SuperHouse/PCBCONVEYOR/Mechanical/Belt Idler Conveyor v6.3mf

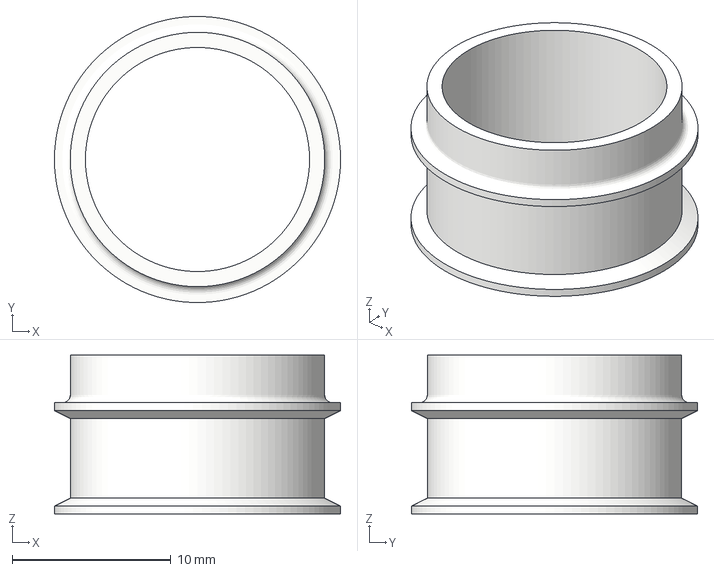
[picture p20: CAD file, 2022-12-20]
Mechanical/Belt Idler Conveyor v6.3mf
18.0 x 18.0 x 10.0 mm
