SuperHouse/PCBCONVEYOR/Mechanical/Front Rail Hole Drilling Template.3mf

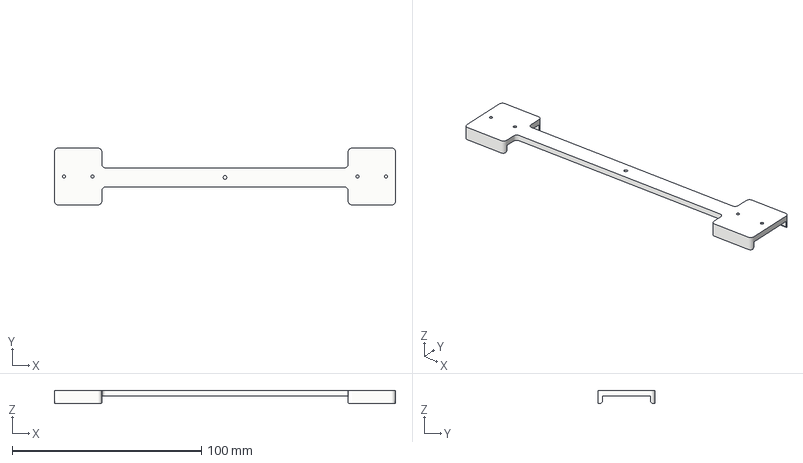
[picture p21: CAD file, 2022-12-20]
Mechanical/Front Rail Hole Drilling Template.3mf
180.0 x 30.0 x 7.00 mm
