SuperHouse/PCBCONVEYOR/Mechanical/GT2 Timing Belt Clamp.3mf

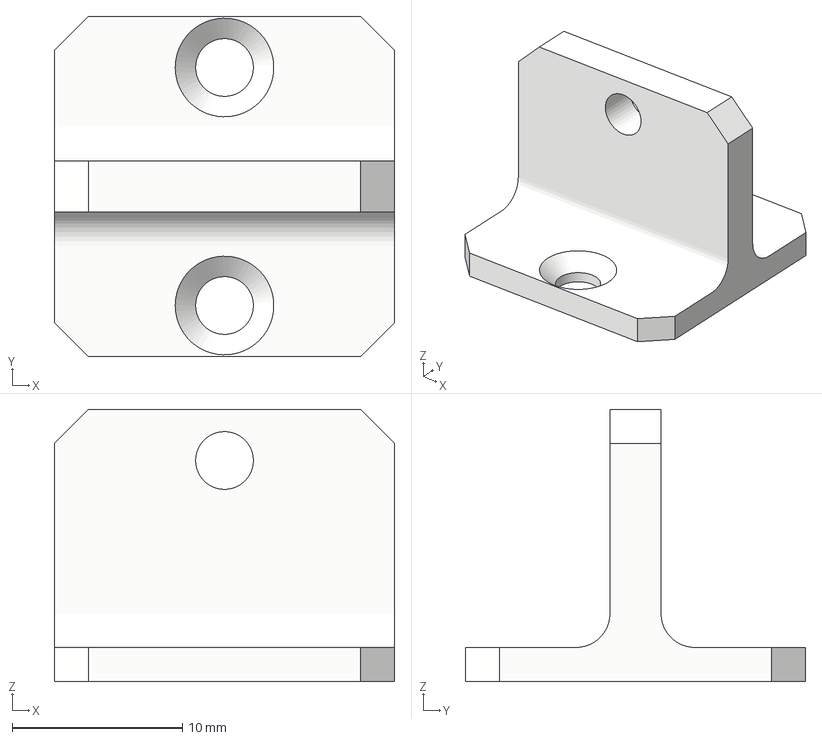
[picture p22: CAD file, 2022-12-20]
Mechanical/GT2 Timing Belt Clamp.3mf
20.0 x 20.0 x 16.0 mm
