SuperHouse/PCBCONVEYOR/Mechanical/PCB Holder PCBCONVEYOR.3mf

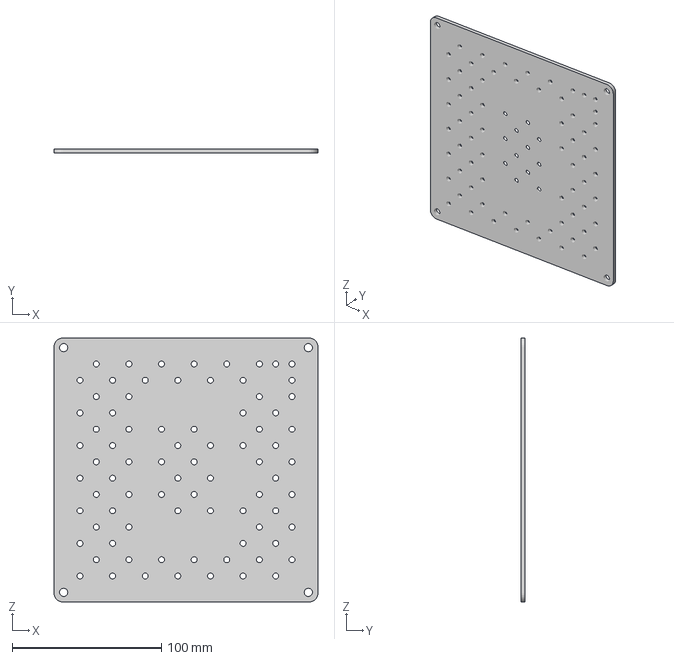
[picture p23: CAD file, 2022-12-20]
Mechanical/PCB Holder PCBCONVEYOR.3mf
177.0 x 3.00 x 177.0 mm
