SuperHouse/PCBCONVEYOR/Mechanical/Limit Switch Cover.3mf

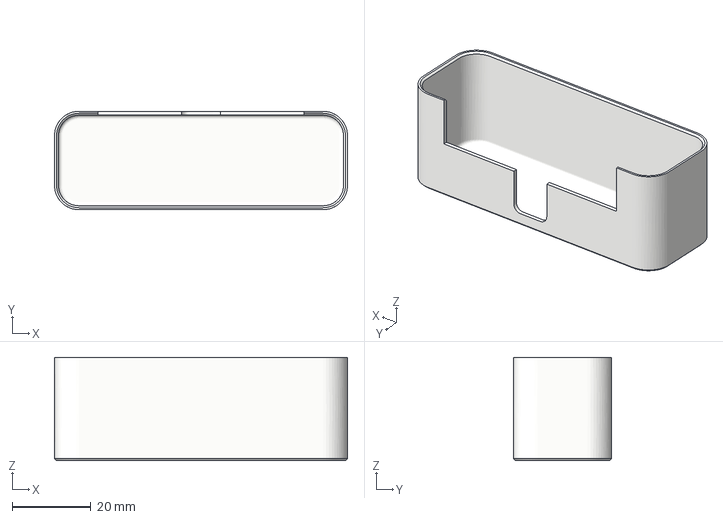
[picture p24: CAD file, 2022-12-20]
Mechanical/Limit Switch Cover.3mf
74.4 x 25.0 x 26.2 mm
