SuperHouse/PCBCONVEYOR/Mechanical/Y Axis Idler Clevis.3mf

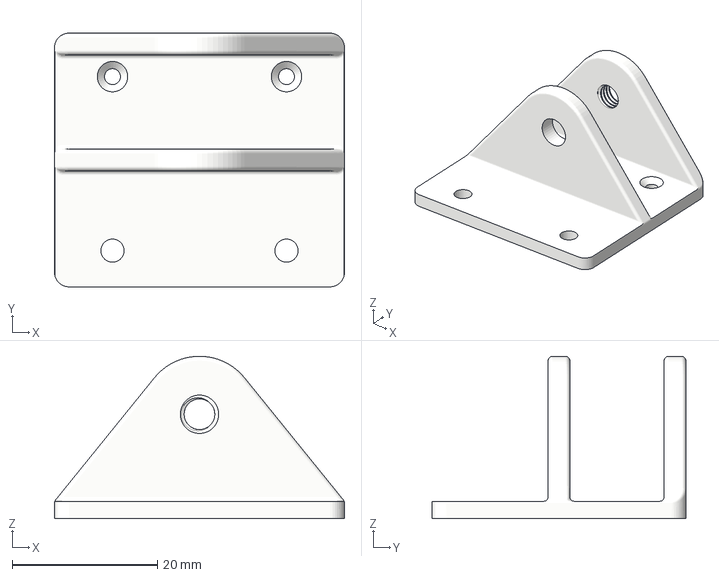
[picture p25: CAD file, 2022-12-20]
Mechanical/Y Axis Idler Clevis.3mf
40.0 x 35.0 x 22.4 mm
