SuperHouse/PCBCONVEYOR/Mechanical/GT2 Timing Belt Clamp Cover.3mf

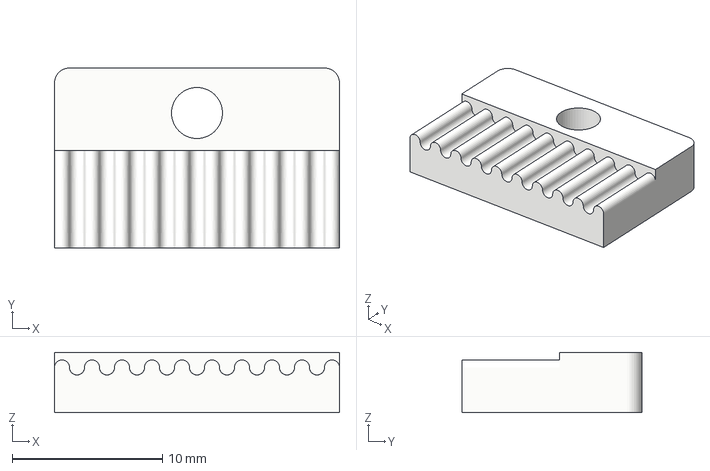
[picture p26: CAD file, 2022-12-20]
Mechanical/GT2 Timing Belt Clamp Cover.3mf
19.0 x 12.0 x 4.00 mm
