SuperHouse/PCBCONVEYOR/Mechanical/Limit Switch Mount.3mf

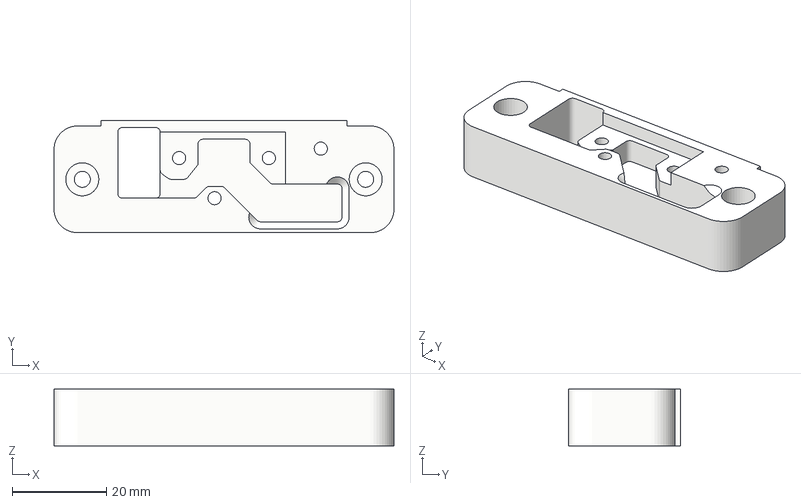
[picture p27: CAD file, 2022-12-20]
Mechanical/Limit Switch Mount.3mf
72.0 x 23.8 x 12.0 mm
