SuperHouse/PCBCONVEYOR/Mechanical/Sensor Probe.3mf

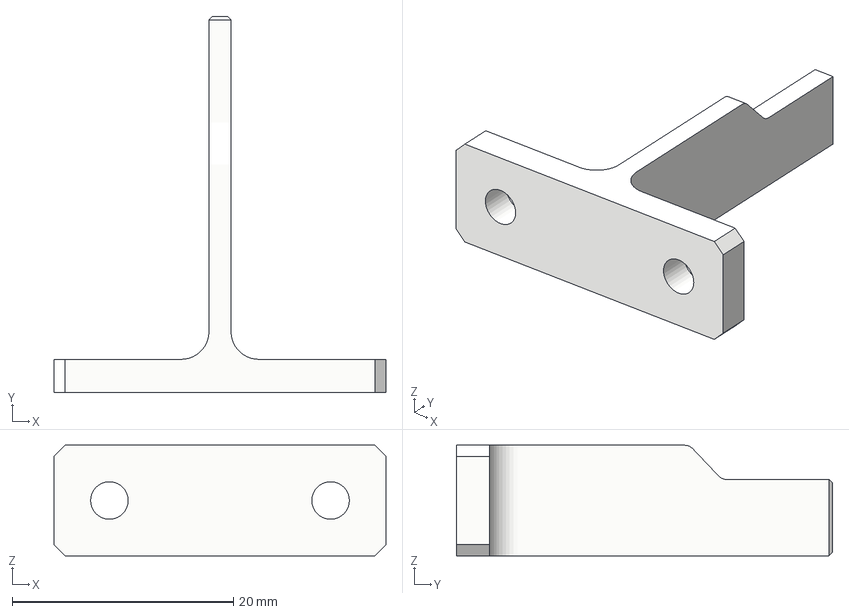
[picture p28: CAD file, 2022-12-20]
Mechanical/Sensor Probe.3mf
30.0 x 34.0 x 10.0 mm
