SuperHouse/PCBCONVEYOR/Mechanical/16mm Idler.3mf

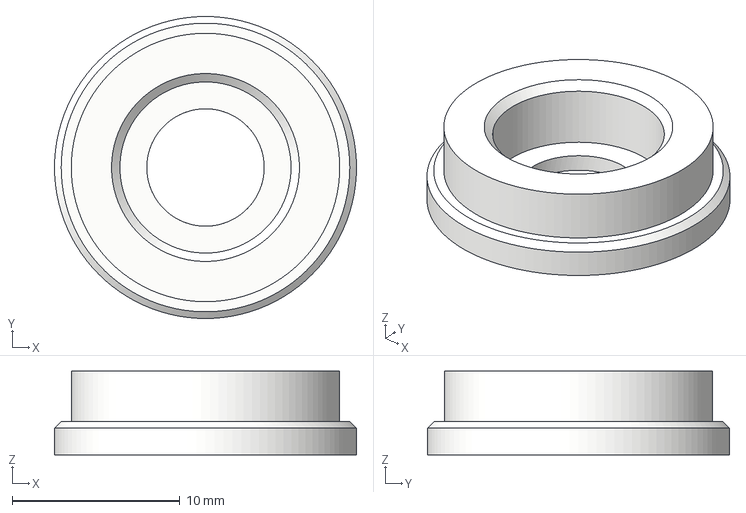
[picture p29: CAD file, 2022-12-20]
Mechanical/16mm Idler.3mf
18.0 x 18.0 x 5.00 mm
