SuperHouse/PCBCONVEYOR/Mechanical/Front Rail Spacer Block.3mf

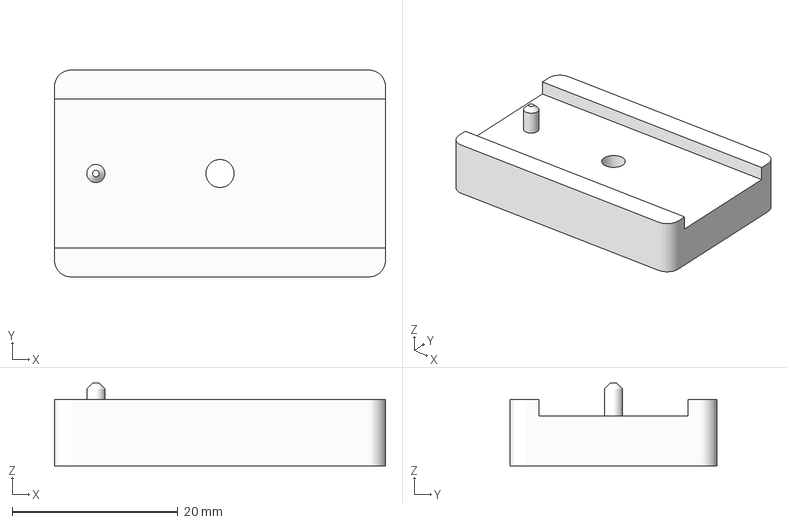
[picture p30: CAD file, 2022-12-20]
Mechanical/Front Rail Spacer Block.3mf
40.0 x 25.0 x 10.0 mm
