SuperHouse/PCBCONVEYOR/Mechanical/2-Way Right Angle.3mf

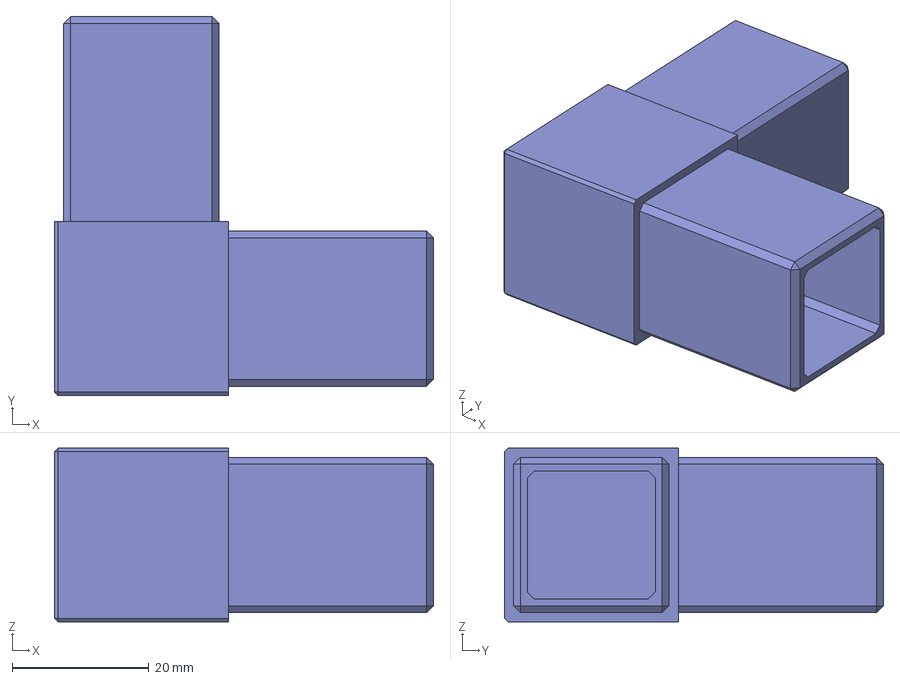
[picture p31: CAD file, 2021-12-23]
Mechanical/2-Way Right Angle.3mf
55.4 x 55.4 x 25.4 mm
